michpro/Arduino_LMeter_shield/LMeter/src/SSD1306Ascii/fonts/Antonio32.h

/*
 *
 * Antonio32
 *
 * created with FontCreator
 * written by F. Maximilian Thiele
 *
 * http://www.apetech.de/fontCreator
 * me@apetech.de
 *
 * File Name           : Antonio32.h
 * Date                : 21.07.2025
 * Font size in bytes  : 53350
 * Font width          : 16
 * Font height         : 32
 * Font first char     : 32
 * Font last char      : 256
 * Font used chars     : 224
 *
 * The font data are defined as
 *
 * struct _FONT_ {
 *     uint16_t   font_Size_in_Bytes_over_all_included_Size_it_self;
 *     uint8_t    font_Width_in_Pixel_for_fixed_drawing;
 *     uint8_t    font_Height_in_Pixel_for_all_characters;
 *     unit8_t    font_First_Char;
 *     uint8_t    font_Char_Count;
 *
 *     uint8_t    font_Char_Widths[font_Last_Char - font_First_Char +1];
 *                  // for each character the separate width in pixels,
 *                  // characters < 128 have an implicit virtual right empty row
 *
 *     uint8_t    font_data[];
 *                  // bit field of all characters
 */

#ifndef ANTONIO32_H
#define ANTONIO32_H

#define ANTONIO32_WIDTH 16
#define ANTONIO32_HEIGHT 32

GLCDFONTDECL(Antonio32) = {
    0xD0, 0x66, // size
    0x10, // width
    0x20, // height
    0x20, // first char
    0xE0, // char count
    
    // char widths
    0x02, 0x02, 0x06, 0x0A, 0x07, 0x14, 0x0A, 0x02, 
    0x04, 0x04, 0x08, 0x07, 0x03, 0x05, 0x02, 0x07, 
    0x08, 0x08, 0x08, 0x08, 0x08, 0x08, 0x08, 0x08, 
    0x08, 0x08, 0x02, 0x04, 0x06, 0x06, 0x06, 0x07, 
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
    0x00, 0x80, 0xC0, 0xC0, 0xC0, 0xC0, 0x80, 0x00, 0xFE, 0xFF, 0xFF, 0x00, 0x80, 0x81, 0x9F, 0x9E, 0x3F, 0xFF, 0xFF, 0x80, 0x81, 0xC1, 0xFF, 0xFF, 0x00, 0x00, 0x01, 0x01, 0x01, 0x00, 0x01, 0x01, // 71
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
    
};

#endif
