michpro/Arduino_LMeter_shield/LMeter/src/SSD1306Ascii/fonts/Callibri31.h

/*
 *
 * new Font
 *
 * created with FontCreator
 * written by F. Maximilian Thiele
 *
 * http://www.apetech.de/fontCreator
 * me@apetech.de
 *
 * File Name           : Callibri31.h
 * Date                : 19.07.2025
 * Font size in bytes  : 32379
 * Font width          : 10
 * Font height         : 29
 * Font first char     : 32
 * Font last char      : 128
 * Font used chars     : 96
 *
 * The font data are defined as
 *
 * struct _FONT_ {
 *     uint16_t   font_Size_in_Bytes_over_all_included_Size_it_self;
 *     uint8_t    font_Width_in_Pixel_for_fixed_drawing;
 *     uint8_t    font_Height_in_Pixel_for_all_characters;
 *     unit8_t    font_First_Char;
 *     uint8_t    font_Char_Count;
 *
 *     uint8_t    font_Char_Widths[font_Last_Char - font_First_Char +1];
 *                  // for each character the separate width in pixels,
 *                  // characters < 128 have an implicit virtual right empty row
 *
 *     uint8_t    font_data[];
 *                  // bit field of all characters
 */

// #include <inttypes.h>
// #include <avr/pgmspace.h>

#ifndef _Callibri31_H
#define _Callibri31_H

#define NEW_FONT_WIDTH 10
#define NEW_FONT_HEIGHT 29

GLCDFONTDECL(Callibri31) = {
    0x7E, 0x7B, // size
    0x0A, // width
    0x1D, // height
    0x20, // first char
    0x60, // char count
    
    // char widths
    0x00, 0x03, 0x08, 0x0E, 0x0D, 0x14, 0x12, 0x03, 0x06, 0x05, 
    0x0B, 0x0D, 0x05, 0x07, 0x03, 0x0C, 0x0E, 0x0C, 0x0C, 0x0C, 
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
    
};

#endif
