michpro/Arduino_LMeter_shield/LMeter/src/SSD1306Ascii/fonts/Droid_Sans_24.h

/*
 *
 * Droid_Sans_24
 *
 * created with FontCreator
 * written by F. Maximilian Thiele
 *
 * http://www.apetech.de/fontCreator
 * me@apetech.de
 *
 * File Name           : Droid_Sans_24.h
 * Date                : 06.03.2013
 * Font size in bytes  : 23777
 * Font width          : 10
 * Font height         : 25
 * Font first char     : 32
 * Font last char      : 128
 * Font used chars     : 96
 *
 * The font data are defined as
 *
 * struct _FONT_ {
 *     uint16_t   font_Size_in_Bytes_over_all_included_Size_it_self;
 *     uint8_t    font_Width_in_Pixel_for_fixed_drawing;
 *     uint8_t    font_Height_in_Pixel_for_all_characters;
 *     unit8_t    font_First_Char;
 *     uint8_t    font_Char_Count;
 *
 *     uint8_t    font_Char_Widths[font_Last_Char - font_First_Char +1];
 *                  // for each character the separate width in pixels,
 *                  // characters < 128 have an implicit virtual right empty row
 *
 *     uint8_t    font_data[];
 *                  // bit field of all characters
 */

#include <inttypes.h>
#ifdef __AVR__
#include <avr/pgmspace.h>
#else
#define PROGMEM
#endif

#ifndef DROID_SANS_24_H
#define DROID_SANS_24_H

#define DROID_SANS_24_WIDTH 10
#define DROID_SANS_24_HEIGHT 25

GLCDFONTDECL(Droid_Sans_24) = {
    0x5C, 0xE1, // size
    0x0A, // width
    0x19, // height
    0x20, // first char
    0x60, // char count
    
    // char widths
    0x00, 0x03, 0x07, 0x0E, 0x0A, 0x12, 0x10, 0x02, 0x06, 0x06, 
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
    
};

#endif
