michpro/Arduino_LMeter_shield/LMeter/src/SSD1306Ascii/fonts/consolas_20pt_bold.h

//
// consolas_20pt_bold
// Font Size: 16x26px
// Created: 17-07-2025 20:39:12
//
#pragma once

// #include <Arduino.h>

// 
// Pseudocode for retrieving data for a specific character:
// 
// bytes_per_char = font_height * (font_width / 8 + ((font_width % 8) ? 1 : 0))
// offset = (ascii_code(character) - ascii_code(' ')) * bytes_per_char
// data = consolas_20pt_bold[offset]
// 

const uint8_t consolas_20pt_bold[] PROGMEM = {
    0x00,0x00,0x00,0x00,0x00,0x00,0x00,0x00,0x00,0x00,0x00,0x00,0x00,0x00,0x00,0x00,
    0x00,0x00,0x00,0x00,0x00,0x00,0x00,0x00,0x00,0x00,0x00,0x00,0x00,0x00,0x00,0x00,
    0x00,0x00,0x00,0x00,0x00,0x00,0x00,0x00,0x00,0x00,0x00,0x00,0x00,0x00,0x00,0x00,
    0x00,0x00,0x00,0x00, // Character 0x20 (32: ' ')
    0x00,0x00,0x00,0x00,0x00,0x00,0xC0,0x01,0xC0,0x01,0xC0,0x01,0xC0,0x01,0xC0,0x01,
    0xC0,0x01,0xC0,0x01,0xC0,0x01,0xC0,0x01,0xC0,0x01,0xC0,0x01,0xC0,0x01,0xC0,0x01,
    0x00,0x00,0xC0,0x00,0xC0,0x01,0xC0,0x01,0xC0,0x01,0x00,0x00,0x00,0x00,0x00,0x00,
    0x00,0x00,0x00,0x00, // Character 0x21 (33: '!')
    0x00,0x00,0x00,0x00,0x00,0x00,0x38,0x0E,0x38,0x0E,0x38,0x0E,0x38,0x06,0x38,0x06,
    0x38,0x06,0x00,0x00,0x00,0x00,0x00,0x00,0x00,0x00,0x00,0x00,0x00,0x00,0x00,0x00,
    0x00,0x00,0x00,0x00,0x00,0x00,0x00,0x00,0x00,0x00,0x00,0x00,0x00,0x00,0x00,0x00,
    0x00,0x00,0x00,0x00, // Character 0x22 (34: '"')
    0x00,0x00,0x00,0x00,0x00,0x00,0x00,0x00,0x70,0x0C,0x30,0x0C,0x30,0x0C,0x30,0x0E,
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
    0x00,0x00,0x00,0x00,0x00,0x00,0x00,0x00,0x00,0x00,0x00,0x00,0x00,0x00,0x00,0x00,
    0x00,0x00,0x00,0x00,0x00,0x00,0x7C,0x00,0xFE,0x30,0xEE,0x39,0xC6,0x3F,0x86,0x1F,
    0x00,0x0E,0x00,0x00,0x00,0x00,0x00,0x00,0x00,0x00,0x00,0x00,0x00,0x00,0x00,0x00,
    0x00,0x00,0x00,0x00, // Character 0x7e (126: '~')
};
